DTVElectronics/cmrat/photos/IMG_9419.jpg

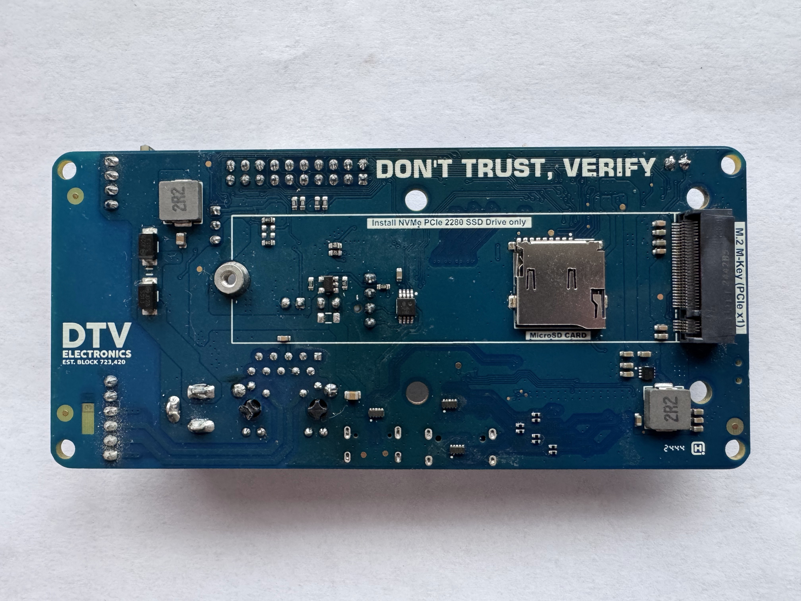
photos/IMG_9419.jpg
