DTVElectronics/cmrat/photos/IMG_9420.jpg

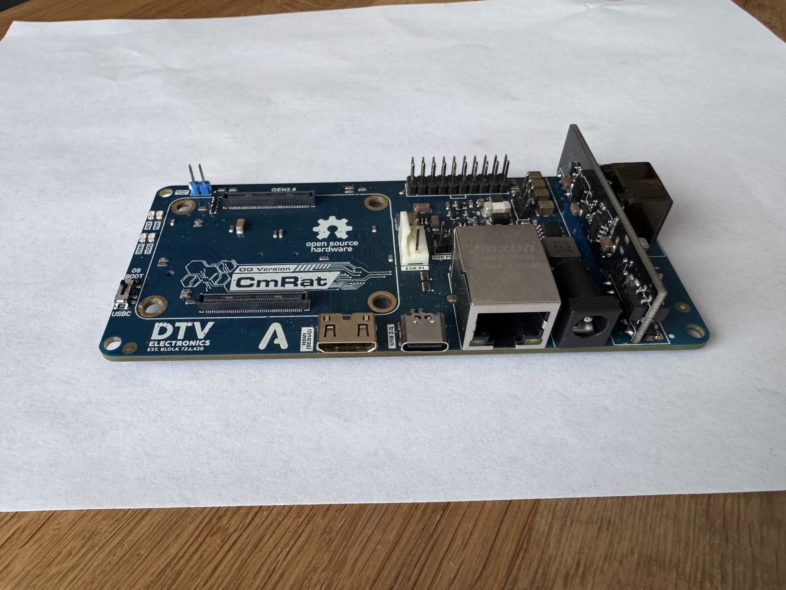
photos/IMG_9420.jpg
