DTVElectronics/cmrat/photos/IMG_9421.jpg

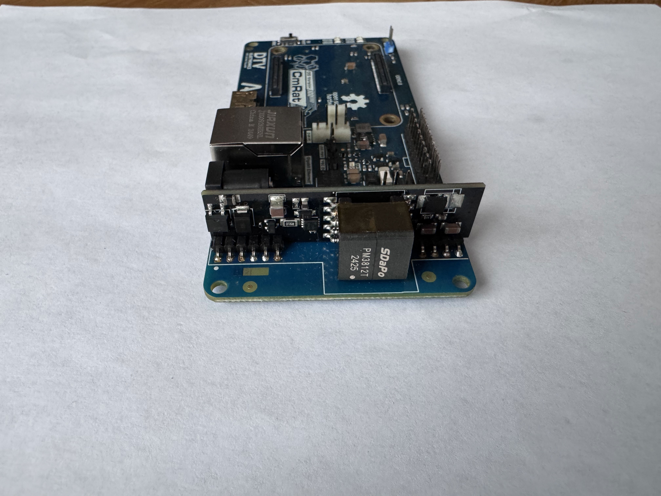
photos/IMG_9421.jpg
