DTVElectronics/cmrat/photos/IMG_9422.jpg

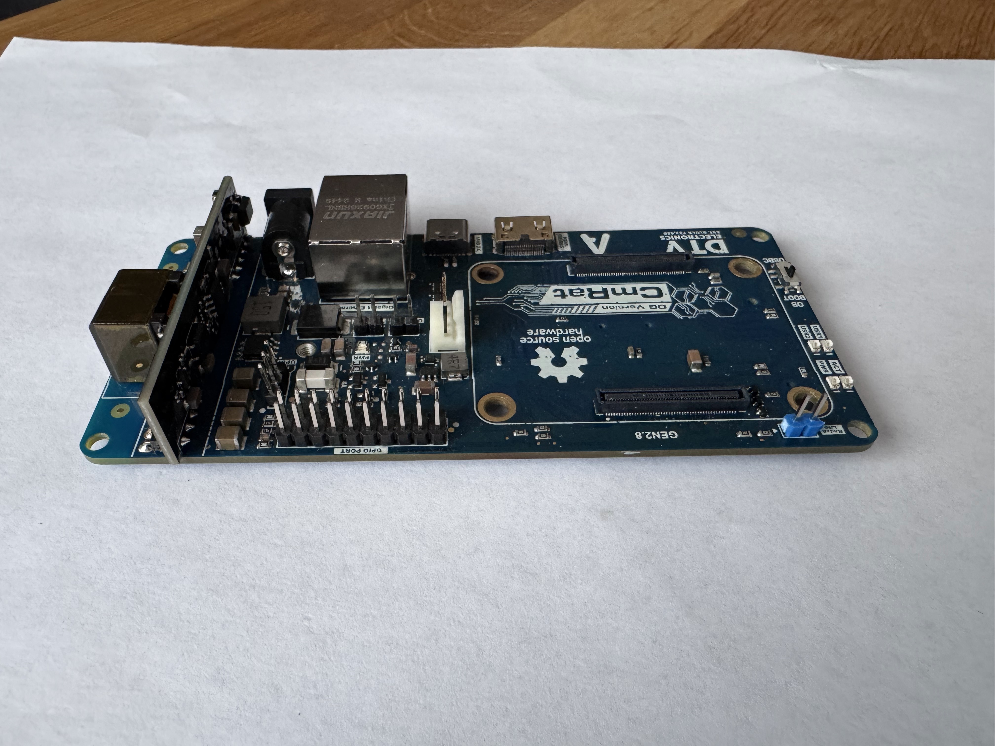
photos/IMG_9422.jpg
