DTVElectronics/cmrat/photos/IMG_9423.jpg

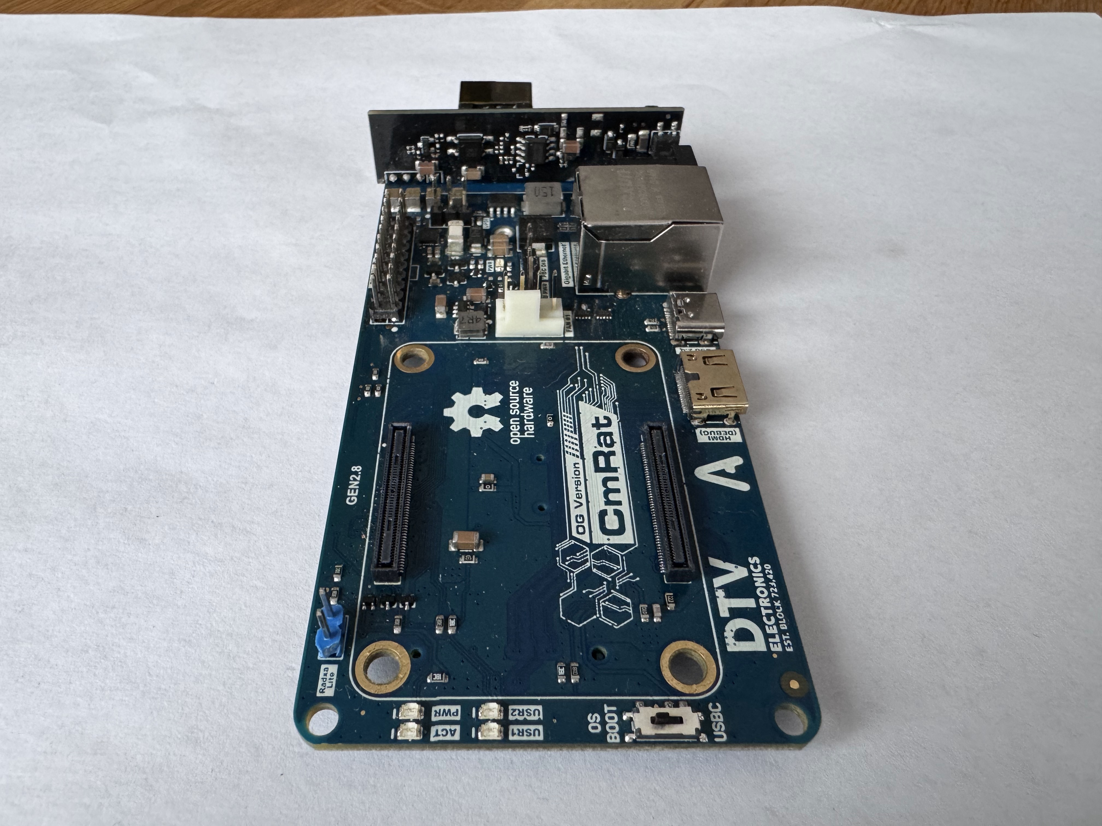
photos/IMG_9423.jpg
