DTVElectronics/cmrat/photos/IMG_9424.jpg

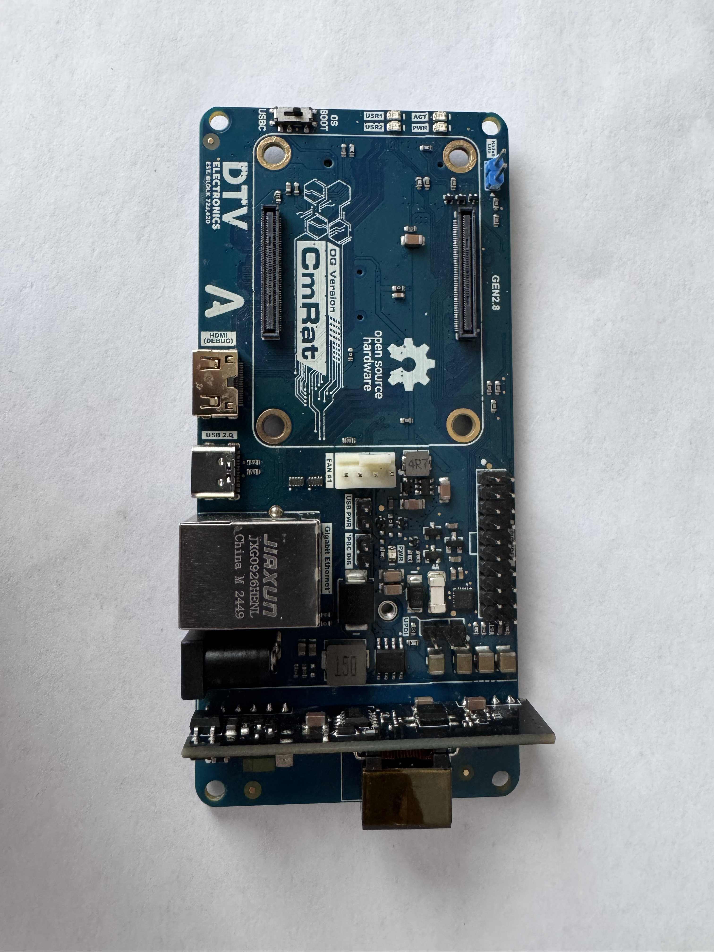
photos/IMG_9424.jpg
