DTVElectronics/cmrat/photos/IMG_9425.jpg

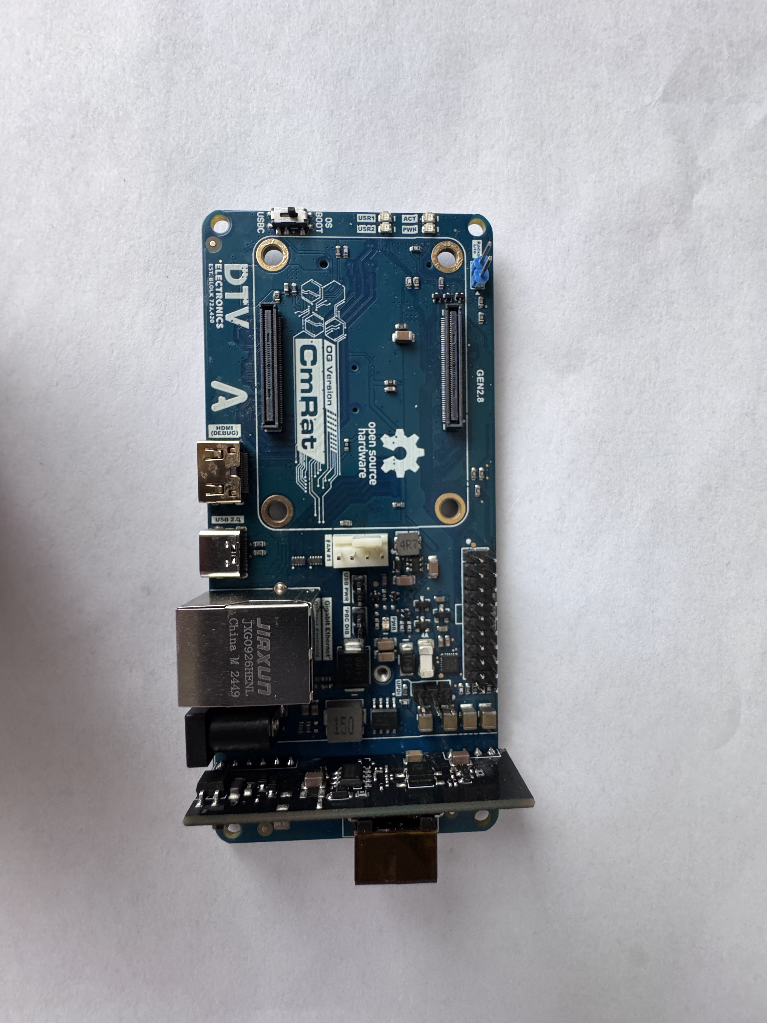
photos/IMG_9425.jpg
