DTVElectronics/cmrat/photos/IMG_9426.jpg

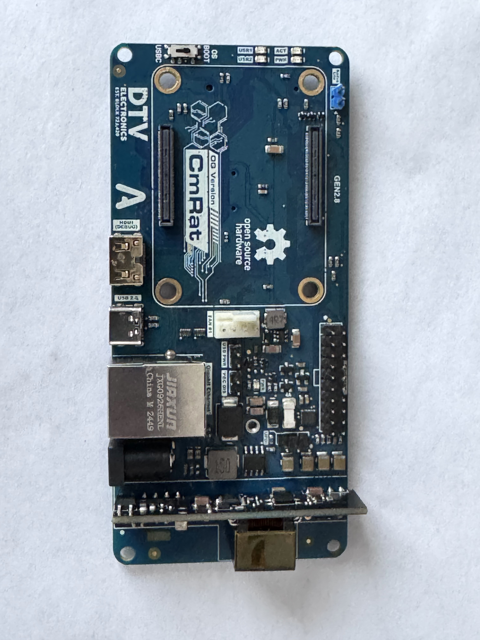
photos/IMG_9426.jpg
